dekuNukem/exixe/resources/current.jpg

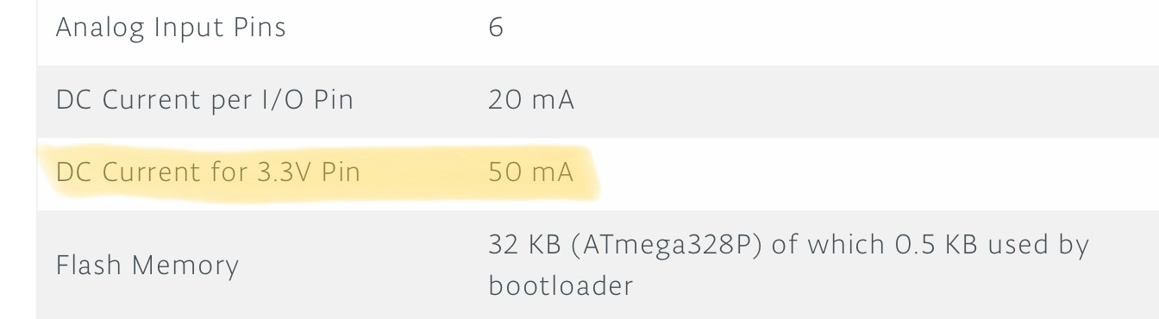
resources/current.jpg
