dekuNukem/exixe/resources/empty_pcb.jpg

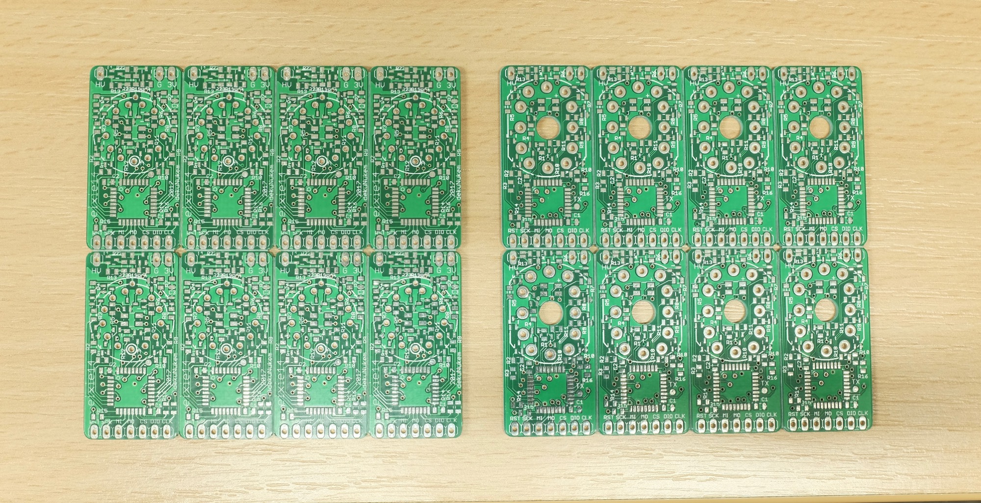
resources/empty_pcb.jpg
