dekuNukem/exixe/resources/example1.jpg

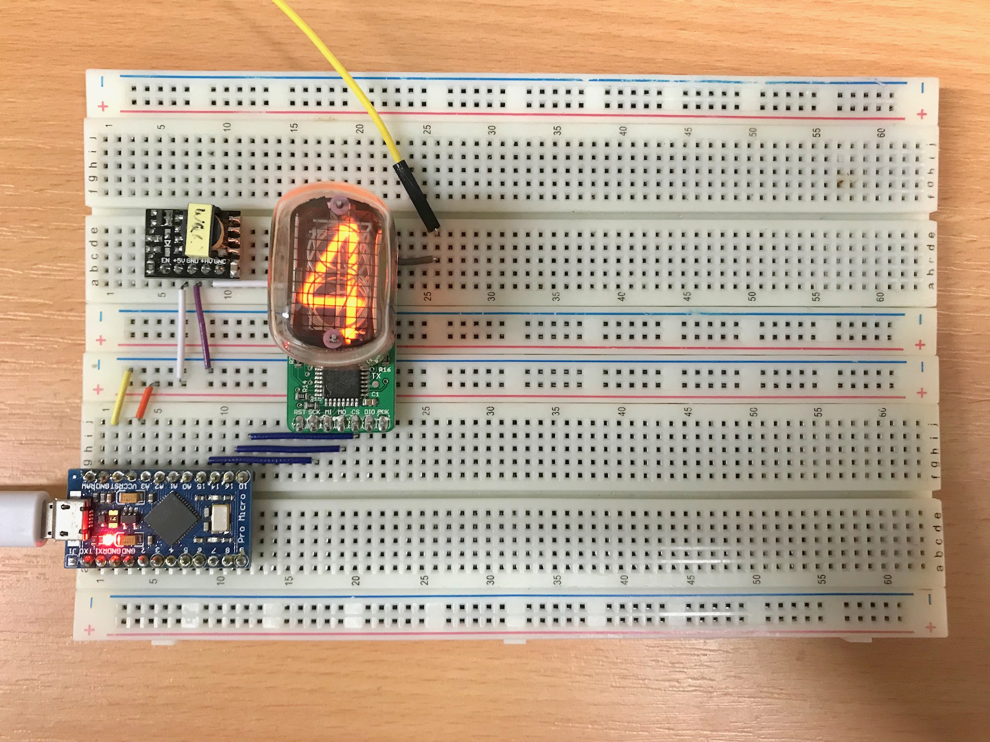
resources/example1.jpg
