dekuNukem/exixe/resources/no_overdrive.jpg

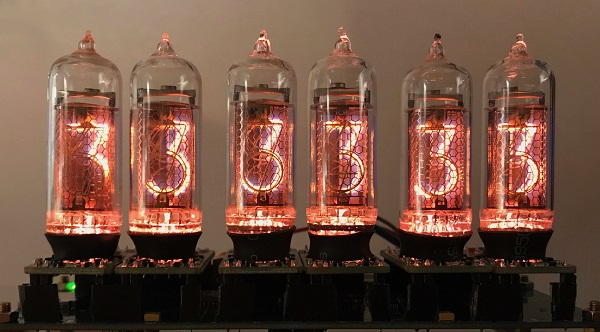
resources/no_overdrive.jpg
