dekuNukem/exixe/resources/with_overdrive.jpg

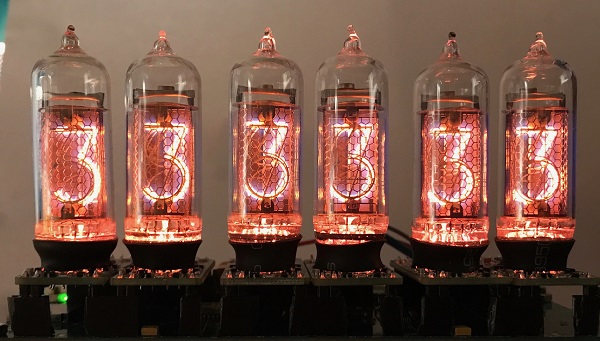
resources/with_overdrive.jpg
