dekuNukem/exixe/resources/Choosing the Right Crystal and Caps for your Design « Adafruit Industries – Makers, hackers, artists, designers and engineers!_files/150x150_005.jpg

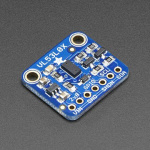
resources/Choosing the Right Crystal and Caps for your Design « Adafruit Industries – Makers, hackers, artists, designers and engineers!_files/150x150_005.jpg
