dekuNukem/exixe/resources/Nixie.pdf

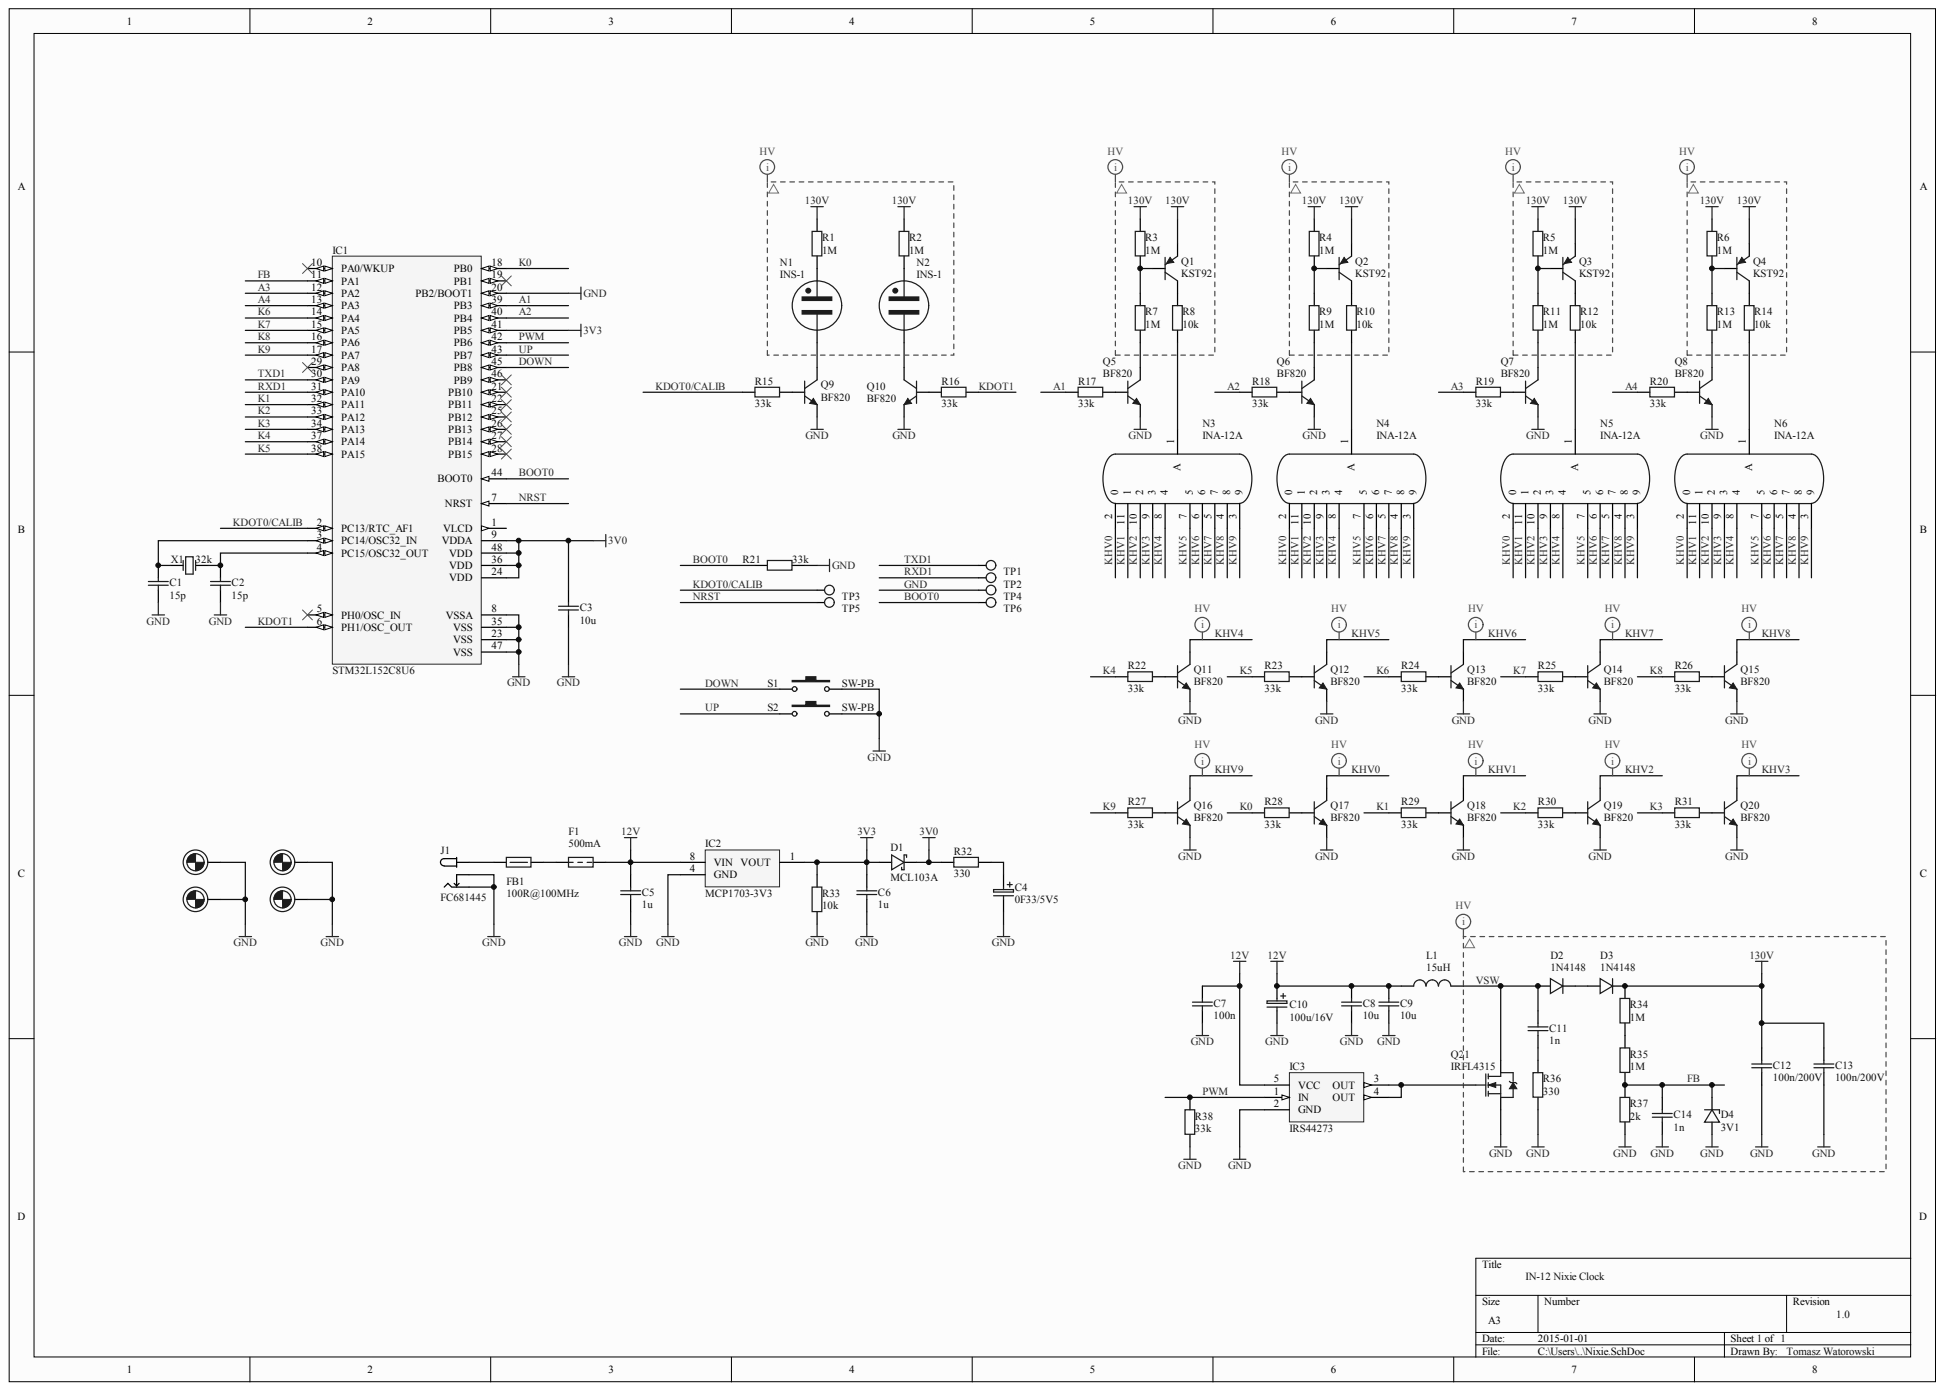
[picture p63: page 1]
