dekuNukem/exixe/pogo_rig/resources/plate2.pdf

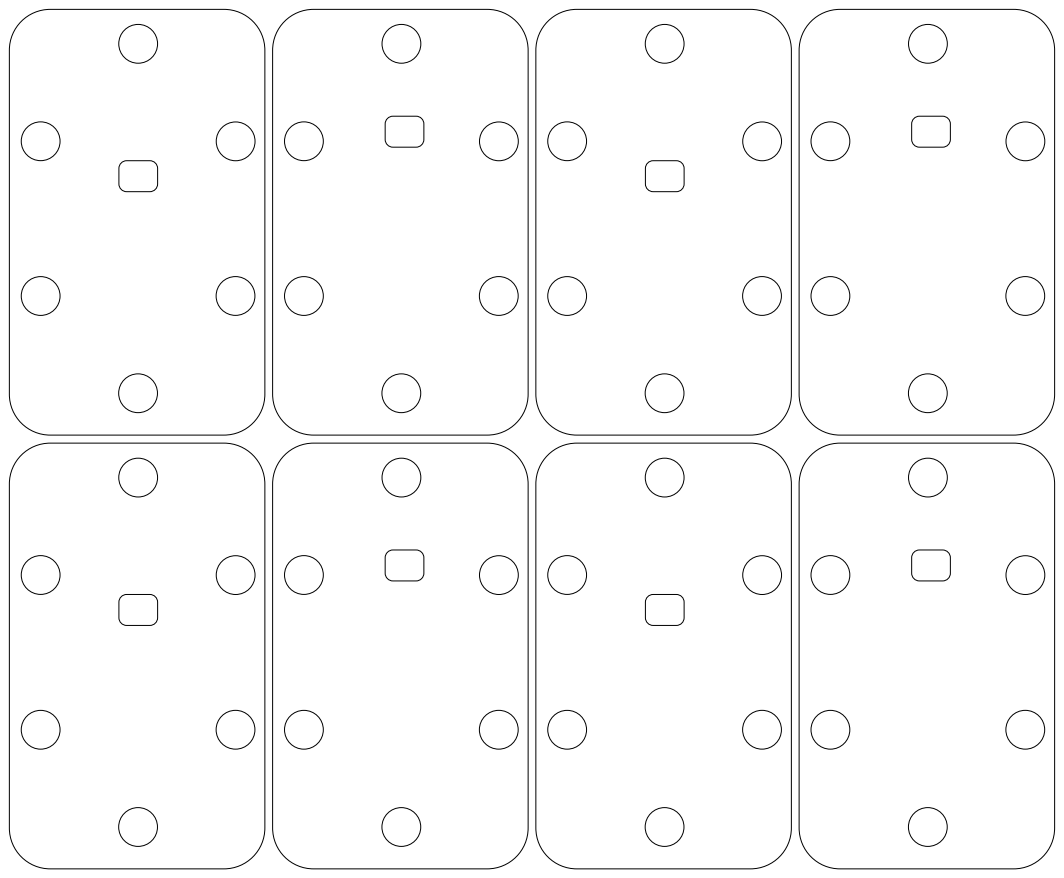
[picture p64: page 1]
