dekuNukem/exixe/arduino_examples/2_loop_digit_simple/2_loop_digit_simple.ino

/*
  exixe modules:
  https://github.com/dekuNukem/exixe

  library docs:
  https://github.com/dekuNukem/exixe/tree/master/arduino_library

  Demo 2: loop digits
*/

#include "exixe.h"

// change this to the cs pin you're using
int cs_pin = 10;
unsigned char count;

exixe my_tube = exixe(cs_pin);

void setup()
{
  my_tube.spi_init();
  my_tube.clear();
}

void loop()
{
  count++;
  my_tube.set_led(127, 0, 127); // purple
  /*
  1st arg: Digit to show, 0 to 9
  2nd arg: Digit brightness, 0 to 127
  3rd arg: Overdrive, 0 disable 1 enable
  */
  my_tube.show_digit(count, 127, 0);
  delay(500);
}
